deveon95/vhdl-teletext/docs/images/hdmi-scanning.png

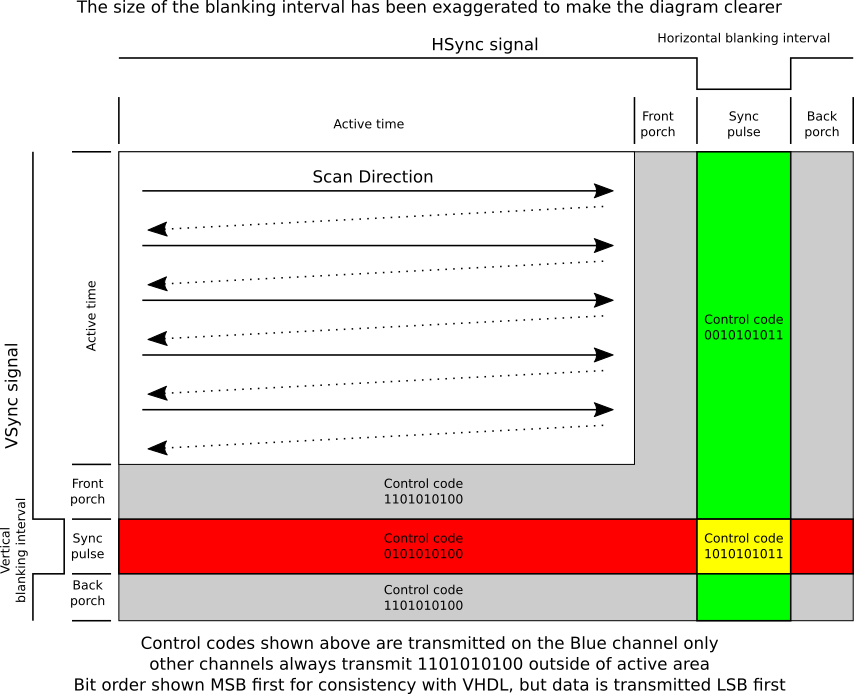
docs/images/hdmi-scanning.png
