deveon95/vhdl-teletext/docs/images/vga-scanning.png

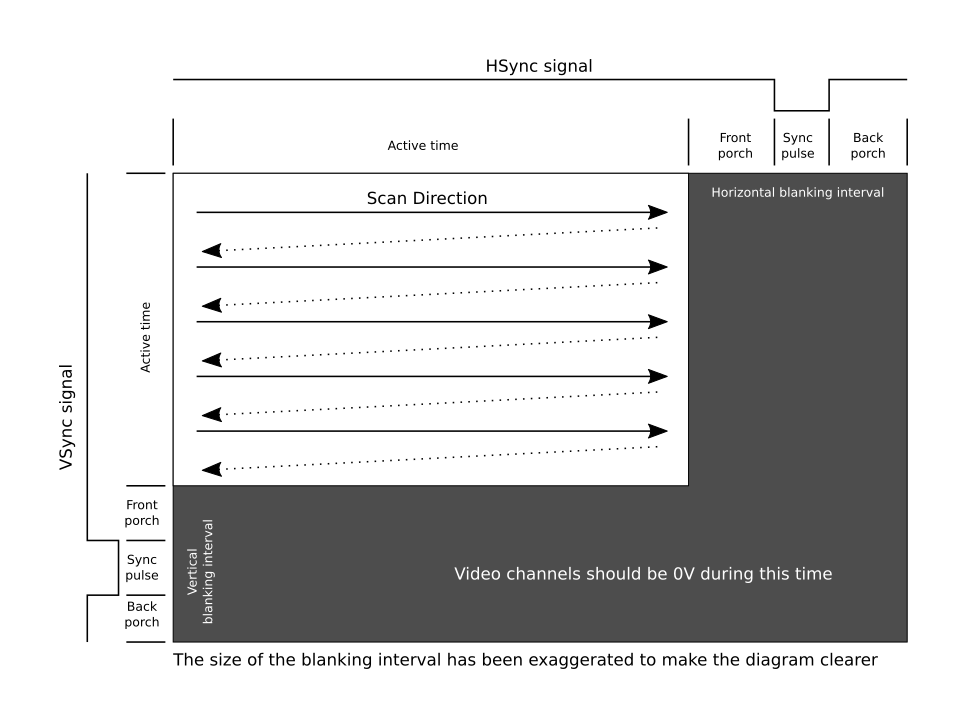
docs/images/vga-scanning.png
