deveon95/vhdl-teletext/src/rtl/TXT_MEMORY_CONTROLLER.vhd

-- TXT_MEMORY_CONTROLLER.vhd
-- Writes processed VBI lines to the dual-port RAM
--
-- Copyright 2020 Nick Schollar
-- This code is subject to the licence in the LICENSE.TXT file in the project directory

library ieee;
use ieee.std_logic_1164.all;
use ieee.numeric_std.all;

entity TXT_MEMORY_CONTROLLER is
    port (
    CLK_27_750       : in  std_logic;
    RESET            : in  std_logic;
    
    WORD_IN          : in  std_logic_vector(17 downto 0);
    WORD_CLOCK_IN    : in  std_logic;
    FRAME_VALID_IN   : in  std_logic;
    UPCOMING_FRAME_IN : in std_logic;
    
    MAGAZINE_IN      : in  std_logic_vector(2 downto 0);
    ROW_IN           : in  std_logic_vector(4 downto 0);
    PAGE_IN          : in  std_logic_vector(7 downto 0);
    SUBCODE_IN       : in  std_logic_vector(12 downto 0);
    CONTROL_BITS_IN  : in  std_logic_vector(10 downto 0);
    
    MEM_DATA_OUT     : out std_logic_vector(6 downto 0);
    MEM_ADDRESS_OUT  : out std_logic_vector(10 downto 0);
    MEM_WREN_OUT     : out std_logic;
    
    
    REQ_MAGAZINE_IN  : in  std_logic_vector(2 downto 0);
    REQ_PAGE_IN      : in  std_logic_vector(7 downto 0);
    REQ_SUBCODE_IN   : in  std_logic_vector(12 downto 0);
    REQ_SUBCODE_SPEC_IN : in std_logic;
    -- Signals for the page number controller
    --LAST_PAGE_OUT    : out std_logic_vector(7 downto 0);
    LAST_SUBCODE_OUT : out std_logic_vector(12 downto 0);
    RED_PAGE_OUT     : out std_logic_vector(10 downto 0);
    GRN_PAGE_OUT     : out std_logic_vector(10 downto 0);
    YEL_PAGE_OUT     : out std_logic_vector(10 downto 0);
    BLU_PAGE_OUT     : out std_logic_vector(10 downto 0);
    IDX_PAGE_OUT     : out std_logic_vector(10 downto 0);
    -- For language selection
    NATIONAL_OPTION_OUT : out std_logic_vector(2 downto 0);
    
    STATUS_IN_1      : in  std_logic_vector(6 downto 0);
    STATUS_IN_2      : in  std_logic_vector(6 downto 0);
    STATUS_IN_3      : in  std_logic_vector(6 downto 0);
    STATUS_IN_4      : in  std_logic_vector(6 downto 0)
    );
    
end entity TXT_MEMORY_CONTROLLER;

architecture RTL of TXT_MEMORY_CONTROLLER is

constant TEXT_COLS : integer := 40;
constant MEMORY_SIZE : integer := 2048;
signal MEMORY_ERASE_REQUIRED : std_logic;
signal VISIBLE_PACKET : std_logic;
signal PAGE_FOUND     : std_logic;          -- Updated at beginning of packet
signal SET_PAGE_FOUND : std_logic;
signal CLEAR_PAGE_FOUND : std_logic;
signal PAGE_FOUND_END : std_logic;          -- Updated at end of packet
signal STATUS_NEEDS_UPDATING : std_logic;
signal STATUS_UPDATED : std_logic;
signal LAST_LOADED_MAGAZINE : std_logic_vector(2 downto 0);
signal LAST_LOADED_PAGE : std_logic_vector(7 downto 0);
signal LAST_LOADED_SUBCODE : std_logic_vector(12 downto 0);
signal LINE_START_ADDRESS : integer range 0 to MEMORY_SIZE - 1;
signal ADDRESS_COUNTER : integer range 0 to MEMORY_SIZE - 1;
signal COLUMN_COUNTER : integer range 0 to TEXT_COLS;
signal ROW_INTEGER : integer range 0 to 31;
signal DESIGNATION : std_logic_vector(3 downto 0);
signal MEM_WREN : std_logic;
signal MEM_DATA : std_logic_vector(6 downto 0);

type STATE_TYPE is (WAIT_FOR_FRAME, RECEIVE_FRAME, NEXT_WORD, ERASE_MEMORY_START, ERASE_MEMORY, UPDATE_STATUS, UPDATE_STATUS_NEXT, IGNORE_FRAME, HAMMING2418_1A, HAMMING2418_1B, HAMMING2418_2A, HAMMING2418_2B, HAMMING2418_3A, HAMMING2418_3B);
signal STATE : STATE_TYPE;
type STATUS_ARRAY_TYPE is array (0 to 7) of std_logic_vector(6 downto 0);
signal STATUS_ARRAY : STATUS_ARRAY_TYPE;
signal STATUS_ARRAY_LAST : STATUS_ARRAY_TYPE;

begin
MAIN: process(CLK_27_750, RESET)
    begin
        if RESET = '1' then
            MEMORY_ERASE_REQUIRED <= '0';
            NATIONAL_OPTION_OUT <= (others => '0');
            MEM_WREN <= '0';
            STATE <= WAIT_FOR_FRAME;
            MEM_DATA <= (others => '0');
            ADDRESS_COUNTER <= 0;
            COLUMN_COUNTER <= 0;
            STATUS_UPDATED <= '0';
            LAST_LOADED_MAGAZINE <= (others => '0');
            LAST_LOADED_PAGE <= (others => '1');
            LAST_LOADED_SUBCODE <= (others => '0');
            PAGE_FOUND_END <= '0';
            RED_PAGE_OUT <= (others => '1');
            GRN_PAGE_OUT <= (others => '1');
            YEL_PAGE_OUT <= (others => '1');
            BLU_PAGE_OUT <= (others => '1');
            IDX_PAGE_OUT <= (others => '1');
            DESIGNATION <= (others => '0');
        elsif rising_edge(CLK_27_750) then
            
            case STATE is
            when WAIT_FOR_FRAME =>
                MEM_WREN <= '0';
                -- Show rolling header when waiting for page. CONTROL_BITS_IN(7) is Magazine Serial
                if FRAME_VALID_IN = '1' and (MAGAZINE_IN = REQ_MAGAZINE_IN or CONTROL_BITS_IN(7) = '1')
                and (ROW_INTEGER = 0) then
                    ADDRESS_COUNTER <= LINE_START_ADDRESS;
                    COLUMN_COUNTER <= 0;
                    MEMORY_ERASE_REQUIRED <= '0';
                    STATE <= RECEIVE_FRAME;
                end if;
                -- Load page when correct page is broadcast
                if FRAME_VALID_IN = '1' and MAGAZINE_IN = REQ_MAGAZINE_IN 
                and (PAGE_IN = REQ_PAGE_IN and (REQ_SUBCODE_IN = SUBCODE_IN or REQ_SUBCODE_SPEC_IN = '0')) then
                    ADDRESS_COUNTER <= LINE_START_ADDRESS;
                    COLUMN_COUNTER <= 0;
                    SET_PAGE_FOUND <= '1';
                    -- Erase page if appropriate bit is set or new page is a different page number. Full Field detection (packet 8/30) required.
                    if PAGE_IN /= LAST_LOADED_PAGE or MAGAZINE_IN /= LAST_LOADED_MAGAZINE then
                        MEMORY_ERASE_REQUIRED <= '1';
                    else
                        MEMORY_ERASE_REQUIRED <= CONTROL_BITS_IN(0);
                    end if;
                    NATIONAL_OPTION_OUT(0) <= CONTROL_BITS_IN(10);
                    NATIONAL_OPTION_OUT(1) <= CONTROL_BITS_IN(9);
                    NATIONAL_OPTION_OUT(2) <= CONTROL_BITS_IN(8);
                    LAST_LOADED_PAGE <= PAGE_IN;
                    LAST_LOADED_SUBCODE <= SUBCODE_IN;
                    LAST_LOADED_MAGAZINE <= MAGAZINE_IN;
                    STATE <= RECEIVE_FRAME;
                end if;
                -- Update status when change in the eight status characters is detected
                if STATUS_NEEDS_UPDATING = '1' and UPCOMING_FRAME_IN = '0' then
                    ADDRESS_COUNTER <= 0;
                    COLUMN_COUNTER <= 0;
                    STATE <= UPDATE_STATUS;
                    STATUS_UPDATED <= '1';
                end if;
            when RECEIVE_FRAME =>
                SET_PAGE_FOUND <= '0';
                if FRAME_VALID_IN = '0' then
                    if MEMORY_ERASE_REQUIRED = '1' and LINE_START_ADDRESS = 8 then
                        STATE <= ERASE_MEMORY_START;
                    else
                        STATE <= WAIT_FOR_FRAME;
                    end if;
                    PAGE_FOUND_END <= PAGE_FOUND;
                elsif WORD_CLOCK_IN = '1' then
                    STATE <= NEXT_WORD;
                    -- IF statement suppresses write enable for header row prior to clock when page has not been found
                    if ROW_INTEGER /= 0 or PAGE_FOUND_END = '0' or ADDRESS_COUNTER >= 32 then
                        -- Enable memory write signal only when current packet is a visible packet
                        MEM_WREN <= VISIBLE_PACKET;
                        MEM_DATA <= WORD_IN(6 downto 0);
                    end if;
                    -- Handle non-visible packets
                    -- Packet X/28 has a Hamming 8/4 coded designation code and the data is all Hamming 24/18 encoded
                    -- Hamming 24/18 decoding is a parallel operation, which can only be completed once all three bytes have been received.
                    -- This means that all three bytes must be written to the RAM in one byte period (32 clock cycles).
                    -- TXT_DATA_PROCESSOR will clock the WORD_CLOCK line once when each Hamming 24/18-decoded word is available
                    -- and TXT_MEMORY_CONTROLLER must write the word to three RAM bytes.
                    if ROW_INTEGER = 28 then
                        DESIGNATION <= WORD_IN(3 downto 0);
                        case COLUMN_COUNTER is
                        when 0 => if WORD_IN(6 downto 0) /= "0000000" and WORD_IN(6 downto 0) /= "0000001" and WORD_IN(6 downto 0) /= "0000011" and WORD_IN(6 downto 0) /= "0000100" then STATE <= IGNORE_FRAME; end if;
                        when 1 =>
                            ADDRESS_COUNTER <= LINE_START_ADDRESS;
                            STATE <= HAMMING2418_1A;
                        when 40 =>
                            STATE <= IGNORE_FRAME;
                        when others =>
                            STATE <= HAMMING2418_1A;
                        end case;
                    
                    -- Packet X/26 has a Hamming 8/4 coded designation code and the data is all Hamming 24/18 encoded
                    elsif ROW_INTEGER = 26 then
                        DESIGNATION <= WORD_IN(3 downto 0);
                        case COLUMN_COUNTER is
                        when 0 => if WORD_IN(6 downto 4) /= "000" then STATE <= IGNORE_FRAME; end if;
                        when 1 =>
                            ADDRESS_COUNTER <= LINE_START_ADDRESS;
                            STATE <= HAMMING2418_1A;
                        when 40 =>
                            STATE <= IGNORE_FRAME;
                        when others =>
                            STATE <= HAMMING2418_1A;
                        end case;
                    
                    -- Fastext editorial links - Hamming code handling is done in TXT_DATA_PROCESSOR and the bits are rearranged
                    -- packet X/27 is entirely Hamming 8/4 encoded
                    elsif ROW_INTEGER = 27 then
                        DESIGNATION <= WORD_IN(3 downto 0);
                        -- Set page number outputs
                        case COLUMN_COUNTER is
                        when 0 => if WORD_IN(6 downto 0) /= "0000000" then STATE <= IGNORE_FRAME; end if;       -- Require designation code 0
                        when 1 => RED_PAGE_OUT(3 downto 0) <= WORD_IN(3) & WORD_IN(2) & WORD_IN(1) & WORD_IN(0);
                        when 2 => RED_PAGE_OUT(7 downto 4) <= WORD_IN(3) & WORD_IN(2) & WORD_IN(1) & WORD_IN(0);
                        when 4 => RED_PAGE_OUT(8) <= WORD_IN(3) XOR MAGAZINE_IN(0);
                        when 6 => RED_PAGE_OUT(10 downto 9) <= (WORD_IN(3) XOR MAGAZINE_IN(2)) & (WORD_IN(2) XOR MAGAZINE_IN(1));
                        when 7 => GRN_PAGE_OUT(3 downto 0) <= WORD_IN(3) & WORD_IN(2) & WORD_IN(1) & WORD_IN(0);
                        when 8 => GRN_PAGE_OUT(7 downto 4) <= WORD_IN(3) & WORD_IN(2) & WORD_IN(1) & WORD_IN(0);
                        when 10 => GRN_PAGE_OUT(8) <= WORD_IN(3) XOR MAGAZINE_IN(0);
                        when 12 => GRN_PAGE_OUT(10 downto 9) <= (WORD_IN(3) XOR MAGAZINE_IN(2)) & (WORD_IN(2) XOR MAGAZINE_IN(1));
                        when 13 => YEL_PAGE_OUT(3 downto 0) <= WORD_IN(3) & WORD_IN(2) & WORD_IN(1) & WORD_IN(0);
                        when 14 => YEL_PAGE_OUT(7 downto 4) <= WORD_IN(3) & WORD_IN(2) & WORD_IN(1) & WORD_IN(0);
                        when 16 => YEL_PAGE_OUT(8) <= WORD_IN(3) XOR MAGAZINE_IN(0);
                        when 18 => YEL_PAGE_OUT(10 downto 9) <= (WORD_IN(3) XOR MAGAZINE_IN(2)) & (WORD_IN(2) XOR MAGAZINE_IN(1));
                        when 19 => BLU_PAGE_OUT(3 downto 0) <= WORD_IN(3) & WORD_IN(2) & WORD_IN(1) & WORD_IN(0);
                        when 20 => BLU_PAGE_OUT(7 downto 4) <= WORD_IN(3) & WORD_IN(2) & WORD_IN(1) & WORD_IN(0);
                        when 22 => BLU_PAGE_OUT(8) <= WORD_IN(3) XOR MAGAZINE_IN(0);
                        when 24 => BLU_PAGE_OUT(10 downto 9) <= (WORD_IN(3) XOR MAGAZINE_IN(2)) & (WORD_IN(2) XOR MAGAZINE_IN(1));
                        when 31 => IDX_PAGE_OUT(3 downto 0) <= WORD_IN(3) & WORD_IN(2) & WORD_IN(1) & WORD_IN(0);
                        when 32 => IDX_PAGE_OUT(7 downto 4) <= WORD_IN(3) & WORD_IN(2) & WORD_IN(1) & WORD_IN(0);
                        when 34 => IDX_PAGE_OUT(8) <= WORD_IN(3) XOR MAGAZINE_IN(0);
                        when 36 => IDX_PAGE_OUT(10 downto 9) <= (WORD_IN(3) XOR MAGAZINE_IN(2)) & (WORD_IN(2) XOR MAGAZINE_IN(1));
                        when others =>
                        end case;
                        -- Set page number outputs to invalid values if a Hamming 8/4 error is detected
                        -- TXT_DATA_PROCESSOR indicates failed bytes by setting bits 4, 5 and 6 in the word
                        if COLUMN_COUNTER <= 36 and WORD_IN(4) = '1' then
                            STATE <= IGNORE_FRAME;
                            RED_PAGE_OUT <= (others => '1');
                            GRN_PAGE_OUT <= (others => '1');
                            YEL_PAGE_OUT <= (others => '1');
                            BLU_PAGE_OUT <= (others => '1');
                            IDX_PAGE_OUT <= (others => '1');
                        end if;
                    end if;
                end if;
            when NEXT_WORD =>
                -- A way of incrementing this for each of the three Hamming 18/24 bytes is needed
                ADDRESS_COUNTER <= ADDRESS_COUNTER + 1;
                COLUMN_COUNTER <= COLUMN_COUNTER + 1;
                MEM_WREN <= '0';
                STATE <= RECEIVE_FRAME;
            when HAMMING2418_1A =>
                MEM_WREN <= '1';
                MEM_DATA <= "1" & WORD_IN(17 downto 12);
                STATE <= HAMMING2418_1B;
            when HAMMING2418_1B =>
                ADDRESS_COUNTER <= ADDRESS_COUNTER + 1;
                COLUMN_COUNTER <= COLUMN_COUNTER + 1;
                MEM_WREN <= '0';
                STATE <= HAMMING2418_2A;
            when HAMMING2418_2A =>
                MEM_WREN <= '1';
                MEM_DATA <= "1" & WORD_IN(11 downto 6);
                STATE <= HAMMING2418_2B;
            when HAMMING2418_2B =>
                ADDRESS_COUNTER <= ADDRESS_COUNTER + 1;
                COLUMN_COUNTER <= COLUMN_COUNTER + 1;
                MEM_WREN <= '0';
                STATE <= HAMMING2418_3A;
            when HAMMING2418_3A =>
                MEM_WREN <= '1';
                MEM_DATA <= "1" & WORD_IN(5 downto 0);
                STATE <= HAMMING2418_3B;
            when HAMMING2418_3B =>
                ADDRESS_COUNTER <= ADDRESS_COUNTER + 1;
                COLUMN_COUNTER <= COLUMN_COUNTER + 1;
                MEM_WREN <= '0';
                STATE <= RECEIVE_FRAME;
            when ERASE_MEMORY_START =>
                ADDRESS_COUNTER <= 40;
                MEM_DATA <= "0100000";
                MEM_WREN <= '1';
                STATE <= ERASE_MEMORY;
            when ERASE_MEMORY =>
                if ADDRESS_COUNTER < MEMORY_SIZE - 1 then
                    ADDRESS_COUNTER <= ADDRESS_COUNTER + 1;
                else
                    STATE <= WAIT_FOR_FRAME;
                end if;
            when UPDATE_STATUS =>
                MEM_DATA <= STATUS_ARRAY(ADDRESS_COUNTER);
                MEM_WREN <= '1';
                STATUS_UPDATED <= '0';
                STATE <= UPDATE_STATUS_NEXT;
            when UPDATE_STATUS_NEXT =>
                MEM_WREN <= '1';
                if ADDRESS_COUNTER = 7 or UPCOMING_FRAME_IN = '1' then
                    STATE <= WAIT_FOR_FRAME;
                else
                    ADDRESS_COUNTER <= ADDRESS_COUNTER + 1;
                    COLUMN_COUNTER <= COLUMN_COUNTER + 1;
                    STATE <= UPDATE_STATUS;
                end if;
            when IGNORE_FRAME =>
                if FRAME_VALID_IN = '0' then
                    STATE <= WAIT_FOR_FRAME;
                end if;
            when others =>
                STATE <= WAIT_FOR_FRAME;
            end case;
        end if;
    end process;
    
    LINE_START_ADDRESS <=       8 when ROW_IN = "00000" else
                          40 *  1 when ROW_IN = "00001" else
                          40 *  2 when ROW_IN = "00010" else
                          40 *  3 when ROW_IN = "00011" else
                          40 *  4 when ROW_IN = "00100" else
                          40 *  5 when ROW_IN = "00101" else
                          40 *  6 when ROW_IN = "00110" else
                          40 *  7 when ROW_IN = "00111" else
                          40 *  8 when ROW_IN = "01000" else
                          40 *  9 when ROW_IN = "01001" else
                          40 * 10 when ROW_IN = "01010" else
                          40 * 11 when ROW_IN = "01011" else
                          40 * 12 when ROW_IN = "01100" else
                          40 * 13 when ROW_IN = "01101" else
                          40 * 14 when ROW_IN = "01110" else
                          40 * 15 when ROW_IN = "01111" else
                          40 * 16 when ROW_IN = "10000" else
                          40 * 17 when ROW_IN = "10001" else
                          40 * 18 when ROW_IN = "10010" else
                          40 * 19 when ROW_IN = "10011" else
                          40 * 20 when ROW_IN = "10100" else
                          40 * 21 when ROW_IN = "10101" else
                          40 * 22 when ROW_IN = "10110" else
                          40 * 23 when ROW_IN = "10111" else
                          40 * 24 when ROW_IN = "11000" else
                          
                          1180 when ROW_IN = "11010" and DESIGNATION = "0000" else
                          1219 when ROW_IN = "11010" and DESIGNATION = "0001" else
                          1258 when ROW_IN = "11010" and DESIGNATION = "0010" else
                          1297 when ROW_IN = "11010" and DESIGNATION = "0011" else
                          1336 when ROW_IN = "11010" and DESIGNATION = "0100" else
                          1375 when ROW_IN = "11010" and DESIGNATION = "0101" else
                          1414 when ROW_IN = "11010" and DESIGNATION = "0110" else
                          1453 when ROW_IN = "11010" and DESIGNATION = "0111" else
                          1492 when ROW_IN = "11010" and DESIGNATION = "1000" else
                          1531 when ROW_IN = "11010" and DESIGNATION = "1001" else
                          1570 when ROW_IN = "11010" and DESIGNATION = "1010" else
                          1609 when ROW_IN = "11010" and DESIGNATION = "1011" else
                          1648 when ROW_IN = "11010" and DESIGNATION = "1100" else
                          1687 when ROW_IN = "11010" and DESIGNATION = "1101" else
                          1726 when ROW_IN = "11010" and DESIGNATION = "1110" else
                          1765 when ROW_IN = "11010" and DESIGNATION = "1111" else
                          1003 when ROW_IN = "11011" else
                          1024 when ROW_IN = "11100" and DESIGNATION = "0100" else
                          1063 when ROW_IN = "11100" and DESIGNATION = "0011" else
                          1102 when ROW_IN = "11100" and DESIGNATION = "0001" else
                          1141 when ROW_IN = "11100" and DESIGNATION = "0000" else
                          0;

    ROW_INTEGER <= to_integer(unsigned(ROW_IN));
    
    VISIBLE_PACKET <= '1' when ROW_INTEGER <= 24 else '0';
    
    MEM_ADDRESS_OUT <= std_logic_vector(to_unsigned(ADDRESS_COUNTER, 11));
    
    STATUS_ARRAY(0) <= "0000111";           -- 0000111 for Alpla White
    STATUS_ARRAY(1) <= STATUS_IN_1;
    STATUS_ARRAY(2) <= STATUS_IN_2;
    STATUS_ARRAY(3) <= STATUS_IN_3;
    STATUS_ARRAY(4) <= STATUS_IN_4;
    STATUS_ARRAY(5) <= "0100000";           -- Space
    STATUS_ARRAY(6) <= "0100000";           -- Space
    STATUS_ARRAY(7) <= "0000010" when PAGE_FOUND = '0' else "0000111";

    CLEAR_PAGE_FOUND <= '0' when LAST_LOADED_PAGE = REQ_PAGE_IN and LAST_LOADED_MAGAZINE = REQ_MAGAZINE_IN and (REQ_SUBCODE_SPEC_IN = '0' or LAST_LOADED_SUBCODE = REQ_SUBCODE_IN) else '1';
    LAST_SUBCODE_OUT <= LAST_LOADED_SUBCODE;
    
    MEM_WREN_OUT <= MEM_WREN;
    MEM_DATA_OUT <= MEM_DATA;
    
PAGE_FOUND_LATCH: process(CLK_27_750, RESET)
    begin
        if RESET = '1' then
            PAGE_FOUND <= '0';
        elsif rising_edge(CLK_27_750) then
            if SET_PAGE_FOUND = '1' then
                PAGE_FOUND <= '1';
            elsif CLEAR_PAGE_FOUND = '1' then
                PAGE_FOUND <= '0';
            end if;
        end if;
    end process;
    
STATUS_ARRAY_MONITOR: process(CLK_27_750, RESET)
    begin
        if RESET = '1' then
            STATUS_NEEDS_UPDATING <= '0';
            STATUS_ARRAY_LAST <= (others => (others => '0'));
        elsif rising_edge(CLK_27_750) then
            if STATUS_ARRAY /= STATUS_ARRAY_LAST then
                STATUS_ARRAY_LAST <= STATUS_ARRAY;
                STATUS_NEEDS_UPDATING <= '1';
            end if;
            if STATUS_UPDATED = '1' then
                STATUS_NEEDS_UPDATING <= '0';
            end if;
        end if;
    end process;
    
end architecture;
