deveon95/vhdl-teletext/src/rtl/CGROM.vhd

library ieee;
use ieee.std_logic_1164.all;
use ieee.numeric_std.all;

entity CGROM is
port (
    ADDRESS_IN : in std_logic_vector(6 downto 0);
    NATIONAL_OPTION_IN : in std_logic_vector(2 downto 0);       -- Need to add the actual characters next
    ROW_SELECT_IN : in std_logic_vector(3 downto 0);
    DATA_OUT : out std_logic_vector(4 downto 0));
end entity CGROM;

architecture RTL of CGROM is
    signal ADDRESS : std_logic_vector(10 downto 0);
    -- NATIONAL_OPTION_IN determines language (15.6.2)
    -- Characters affected are 0x23, 0x24, 0x40, 0x5B, 0x5C, 0x5D, 0x5E, 0x5F, 0x60, 0x7B, 0x7C, 0x7D, 0x7E
    -- Languages are:
    -- 000 English
    -- 001 German
    -- 010 Swedish / Finnish / Hungarian
    -- 011 Italian
    -- 100 French
    -- 101 Portuguese/Spanish
    -- 110 Czech/Slovak
    
begin
    ADDRESS <= ADDRESS_IN & ROW_SELECT_IN;
    
    DATA_OUT <= "00000" when ADDRESS = B"0100000_0000" else
                "00000" when ADDRESS = B"0100000_0001" else
                "00000" when ADDRESS = B"0100000_0010" else
                "00000" when ADDRESS = B"0100000_0011" else
                "00000" when ADDRESS = B"0100000_0100" else
                "00000" when ADDRESS = B"0100000_0101" else
                "00000" when ADDRESS = B"0100000_0110" else
                "00000" when ADDRESS = B"0100000_0111" else
                "00000" when ADDRESS = B"0100000_1000" else
                
                "00100" when ADDRESS = B"0100001_0000" else
                "00100" when ADDRESS = B"0100001_0001" else
                "00100" when ADDRESS = B"0100001_0010" else
                "00100" when ADDRESS = B"0100001_0011" else
                "00000" when ADDRESS = B"0100001_0100" else
                "00100" when ADDRESS = B"0100001_0101" else
                "00000" when ADDRESS = B"0100001_0110" else
                "00000" when ADDRESS = B"0100001_0111" else
                "00000" when ADDRESS = B"0100001_1000" else
                
                "00000" when ADDRESS = B"0100010_0000" else
                "01010" when ADDRESS = B"0100010_0001" else
                "01010" when ADDRESS = B"0100010_0010" else
                "01010" when ADDRESS = B"0100010_0011" else
                "00000" when ADDRESS = B"0100010_0100" else
                "00000" when ADDRESS = B"0100010_0101" else
                "00000" when ADDRESS = B"0100010_0110" else
                "00000" when ADDRESS = B"0100010_0111" else
                "00000" when ADDRESS = B"0100010_1000" else
                -- Character 0x23
                -- English, Italian
                "00110" when ADDRESS = B"0100011_0000" and (NATIONAL_OPTION_IN = B"000" or NATIONAL_OPTION_IN = B"011" or NATIONAL_OPTION_IN = B"111") else
                "01001" when ADDRESS = B"0100011_0001" and (NATIONAL_OPTION_IN = B"000" or NATIONAL_OPTION_IN = B"011" or NATIONAL_OPTION_IN = B"111") else
                "01000" when ADDRESS = B"0100011_0010" and (NATIONAL_OPTION_IN = B"000" or NATIONAL_OPTION_IN = B"011" or NATIONAL_OPTION_IN = B"111") else
                "01110" when ADDRESS = B"0100011_0011" and (NATIONAL_OPTION_IN = B"000" or NATIONAL_OPTION_IN = B"011" or NATIONAL_OPTION_IN = B"111") else
                "01000" when ADDRESS = B"0100011_0100" and (NATIONAL_OPTION_IN = B"000" or NATIONAL_OPTION_IN = B"011" or NATIONAL_OPTION_IN = B"111") else
                "01000" when ADDRESS = B"0100011_0101" and (NATIONAL_OPTION_IN = B"000" or NATIONAL_OPTION_IN = B"011" or NATIONAL_OPTION_IN = B"111") else
                "10111" when ADDRESS = B"0100011_0110" and (NATIONAL_OPTION_IN = B"000" or NATIONAL_OPTION_IN = B"011" or NATIONAL_OPTION_IN = B"111") else
                "00000" when ADDRESS = B"0100011_0111" and (NATIONAL_OPTION_IN = B"000" or NATIONAL_OPTION_IN = B"011" or NATIONAL_OPTION_IN = B"111") else
                "00000" when ADDRESS = B"0100011_1000" and (NATIONAL_OPTION_IN = B"000" or NATIONAL_OPTION_IN = B"011" or NATIONAL_OPTION_IN = B"111") else
                -- German, Swedish/Finnish, Czech/Slovak
                "01010" when ADDRESS = B"0100011_0000" and (NATIONAL_OPTION_IN = B"001" or NATIONAL_OPTION_IN = B"010" or NATIONAL_OPTION_IN = B"110") else
                "11111" when ADDRESS = B"0100011_0001" and (NATIONAL_OPTION_IN = B"001" or NATIONAL_OPTION_IN = B"010" or NATIONAL_OPTION_IN = B"110") else
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
                -- French
                "00000" when ADDRESS = B"1111110_0000" and (NATIONAL_OPTION_IN = B"100") else
                "00000" when ADDRESS = B"1111110_0001" and (NATIONAL_OPTION_IN = B"100") else
                "01111" when ADDRESS = B"1111110_0010" and (NATIONAL_OPTION_IN = B"100") else
                "10000" when ADDRESS = B"1111110_0011" and (NATIONAL_OPTION_IN = B"100") else
                "10000" when ADDRESS = B"1111110_0100" and (NATIONAL_OPTION_IN = B"100") else
                "10000" when ADDRESS = B"1111110_0101" and (NATIONAL_OPTION_IN = B"100") else
                "01111" when ADDRESS = B"1111110_0110" and (NATIONAL_OPTION_IN = B"100") else
                "00100" when ADDRESS = B"1111110_0111" and (NATIONAL_OPTION_IN = B"100") else
                "01000" when ADDRESS = B"1111110_1000" and (NATIONAL_OPTION_IN = B"100") else
                -- Portuguese/Spanish
                "01000" when ADDRESS = B"1111110_0000" and (NATIONAL_OPTION_IN = B"101") else
                "00100" when ADDRESS = B"1111110_0001" and (NATIONAL_OPTION_IN = B"101") else
                "01110" when ADDRESS = B"1111110_0010" and (NATIONAL_OPTION_IN = B"101") else
                "00001" when ADDRESS = B"1111110_0011" and (NATIONAL_OPTION_IN = B"101") else
                "01111" when ADDRESS = B"1111110_0100" and (NATIONAL_OPTION_IN = B"101") else
                "10001" when ADDRESS = B"1111110_0101" and (NATIONAL_OPTION_IN = B"101") else
                "01111" when ADDRESS = B"1111110_0110" and (NATIONAL_OPTION_IN = B"101") else
                "00000" when ADDRESS = B"1111110_0111" and (NATIONAL_OPTION_IN = B"101") else
                "00000" when ADDRESS = B"1111110_1000" and (NATIONAL_OPTION_IN = B"101") else
                -- Czech/Slovak
                "01010" when ADDRESS = B"1111110_0000" and (NATIONAL_OPTION_IN = B"110") else
                "00100" when ADDRESS = B"1111110_0001" and (NATIONAL_OPTION_IN = B"110") else
                "01111" when ADDRESS = B"1111110_0010" and (NATIONAL_OPTION_IN = B"110") else
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
