deveon95/vhdl-teletext/src/rtl/intosc/intosc_inst.vhd

	component intosc is
		port (
			oscena : in  std_logic := 'X'; -- oscena
			clkout : out std_logic         -- clk
		);
	end component intosc;

	u0 : component intosc
		port map (
			oscena => CONNECTED_TO_oscena, -- oscena.oscena
			clkout => CONNECTED_TO_clkout  -- clkout.clk
		);
